snack-o-saurus/TPDA-SpaceArcade/Documentation/Pictures/nerfcomplete2.jpeg

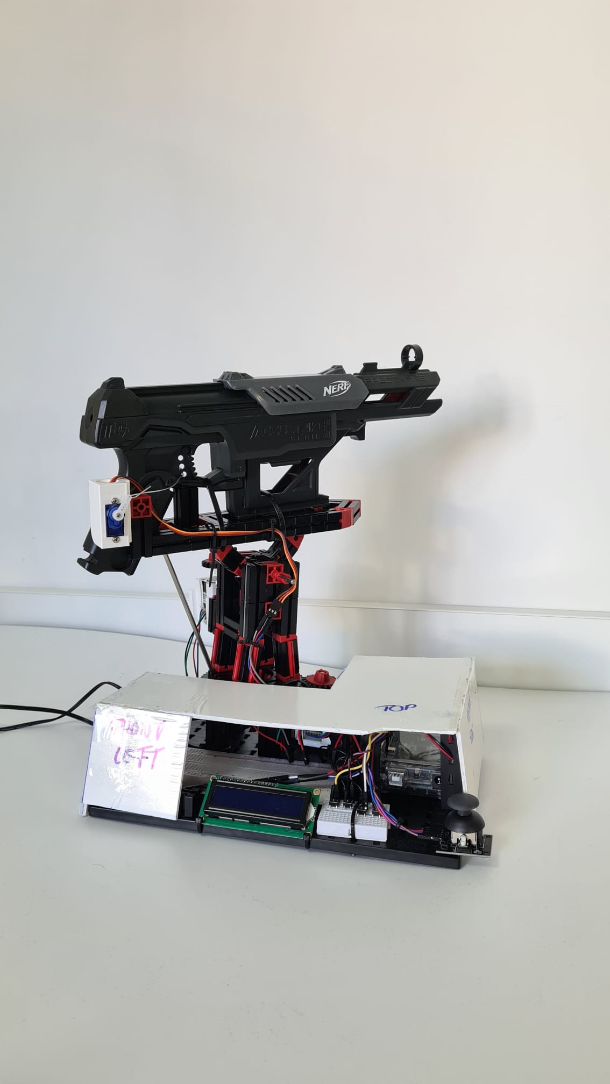
Documentation/Pictures/nerfcomplete2.jpeg
