snack-o-saurus/TPDA-SpaceArcade/Documentation/Pictures/nerfcomplete3.jpeg

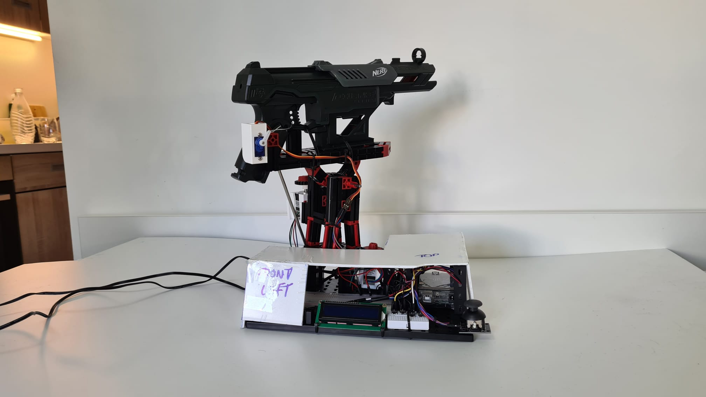
Documentation/Pictures/nerfcomplete3.jpeg
