snack-o-saurus/TPDA-SpaceArcade/Documentation/Pictures/Teiletest aus dem Druck-1/Teiltest-MEGA-1.jpeg

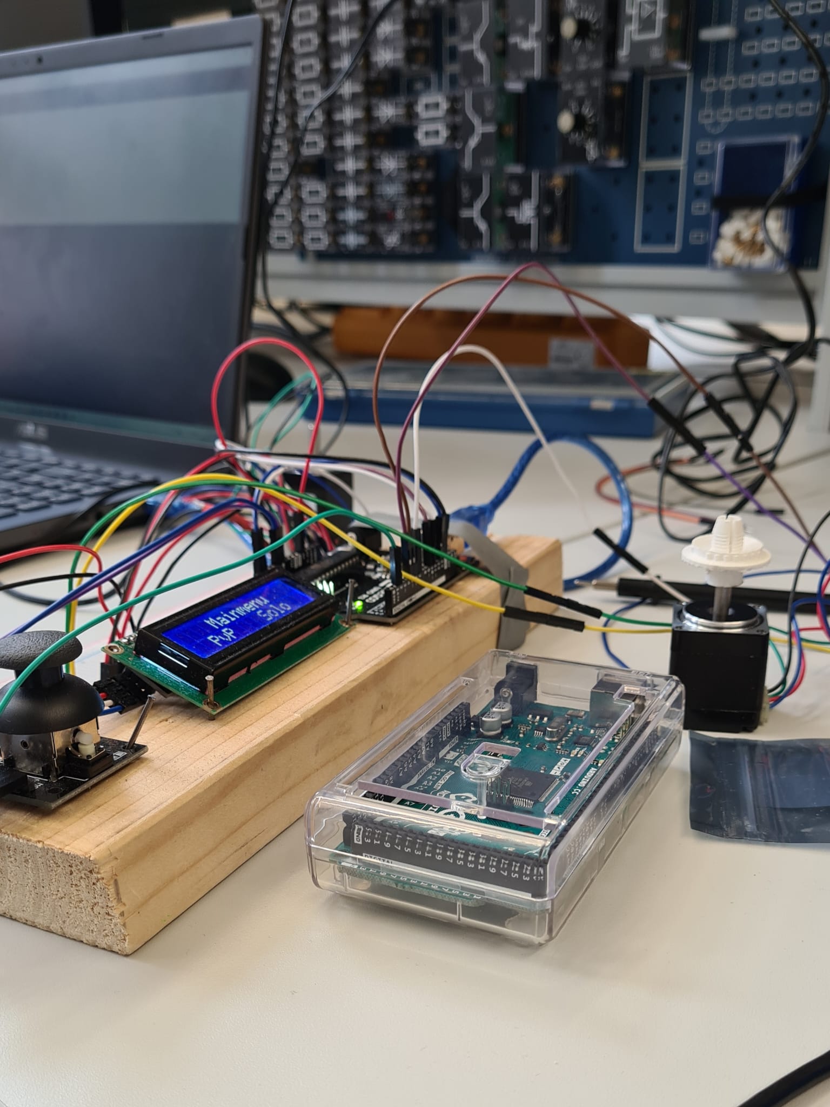
Documentation/Pictures/Teiletest aus dem Druck-1/Teiltest-MEGA-1.jpeg
