snack-o-saurus/TPDA-SpaceArcade/Documentation/Pictures/Teiletest aus dem Druck-1/Teiltest-Zahnradadapter-MEGA.jpeg

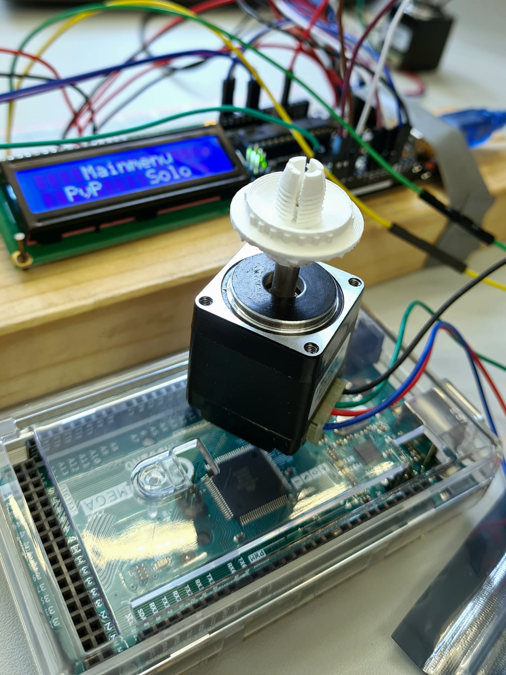
Documentation/Pictures/Teiletest aus dem Druck-1/Teiltest-Zahnradadapter-MEGA.jpeg
