snack-o-saurus/TPDA-SpaceArcade/Documentation/Pictures/Turmkonstruktion/Fischertechnik-Turret-1.jpeg

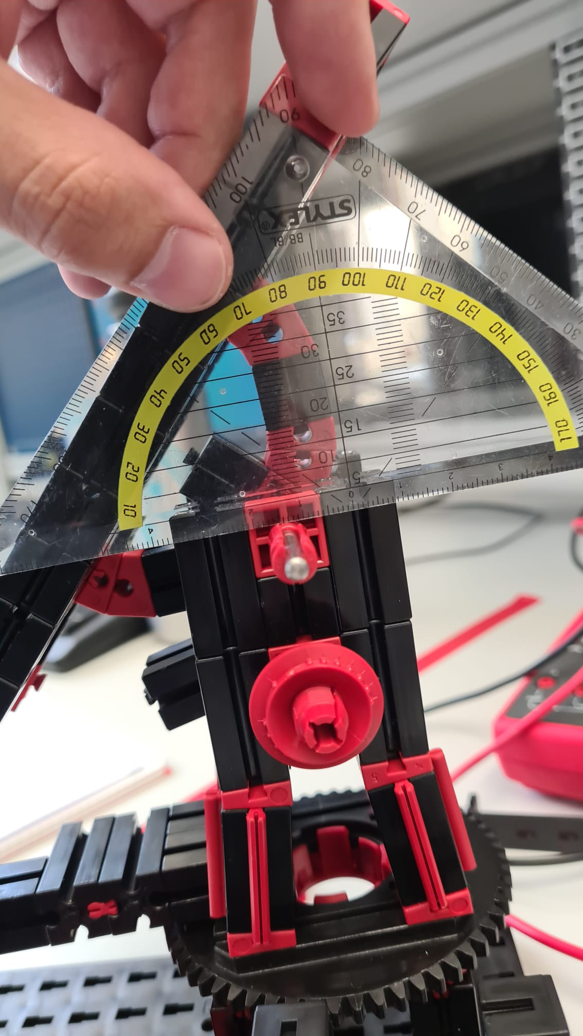
Documentation/Pictures/Turmkonstruktion/Fischertechnik-Turret-1.jpeg
