snack-o-saurus/TPDA-SpaceArcade/Documentation/Pictures/Turmkonstruktion/Fischertechnik-Turret-2.jpeg

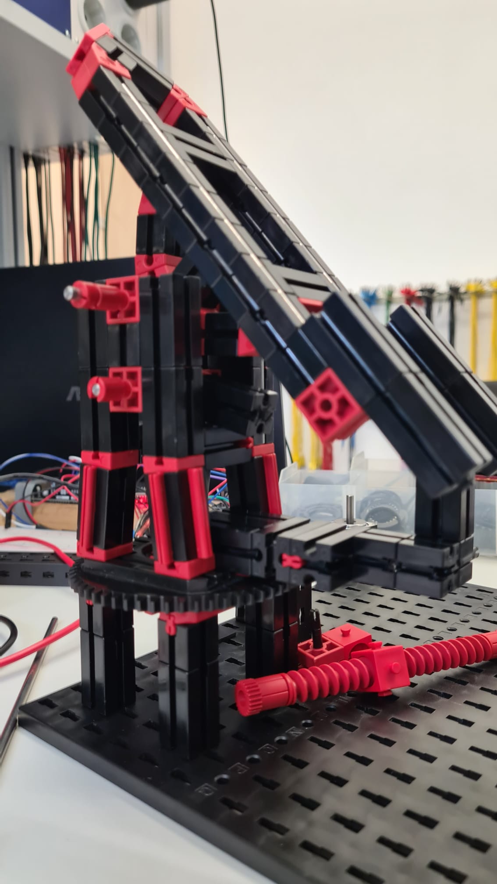
Documentation/Pictures/Turmkonstruktion/Fischertechnik-Turret-2.jpeg
