snack-o-saurus/TPDA-SpaceArcade/Documentation/Pictures/Turmkonstruktion/Fischertechnik-Turret-3.jpeg

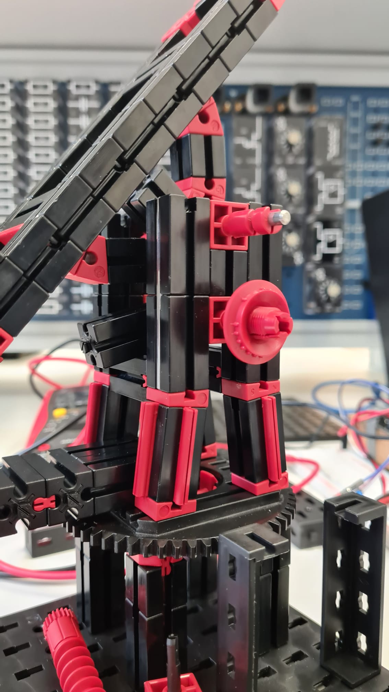
Documentation/Pictures/Turmkonstruktion/Fischertechnik-Turret-3.jpeg
