snack-o-saurus/TPDA-SpaceArcade/Documentation/Pictures/Turmkonstruktion/Fischertechnik-Turret-4.jpeg

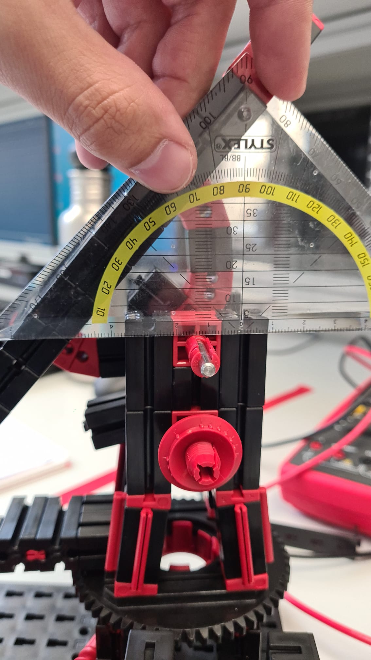
Documentation/Pictures/Turmkonstruktion/Fischertechnik-Turret-4.jpeg
