snack-o-saurus/TPDA-SpaceArcade/models/Druck01_v3/GCode-Sliceshot.png

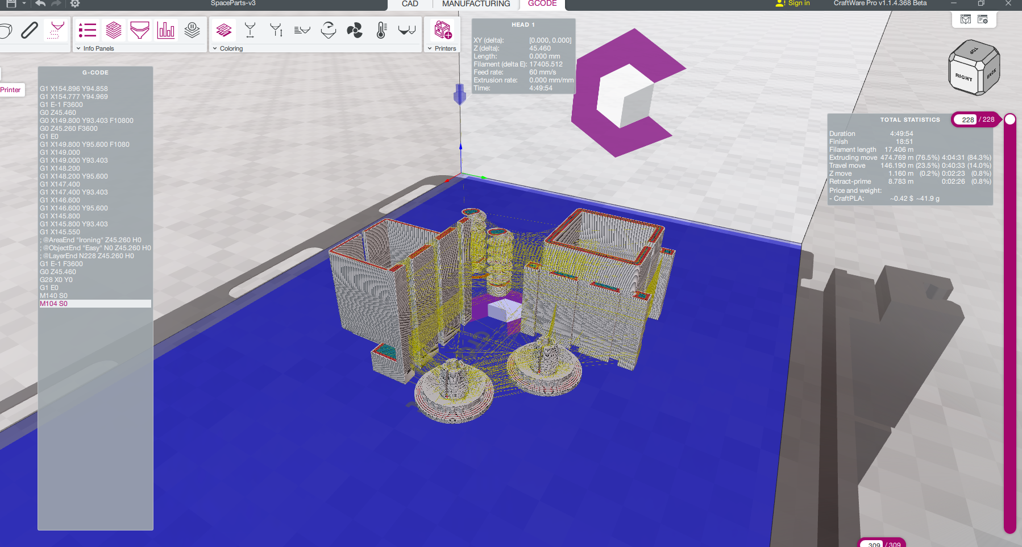
models/Druck01_v3/GCode-Sliceshot.png
