snack-o-saurus/TPDA-SpaceArcade/models/Druck01_v3/MotorPAN-case_2022-Jun-07_10-06-19AM-000_CustomizedView7136299601.png

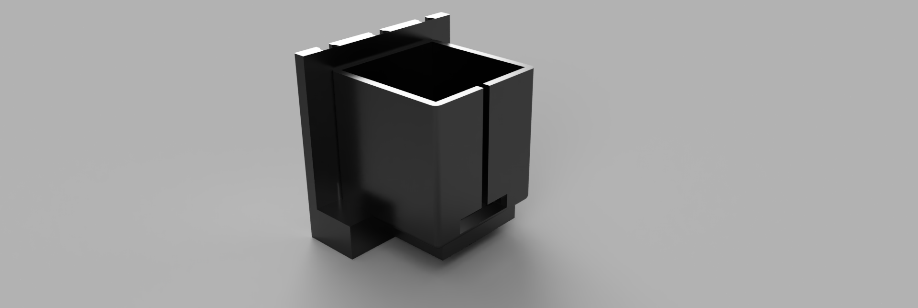
models/Druck01_v3/MotorPAN-case_2022-Jun-07_10-06-19AM-000_CustomizedView7136299601.png
