snack-o-saurus/TPDA-SpaceArcade/models/Druck01_v3/PartSummary-Render-TILT.PNG

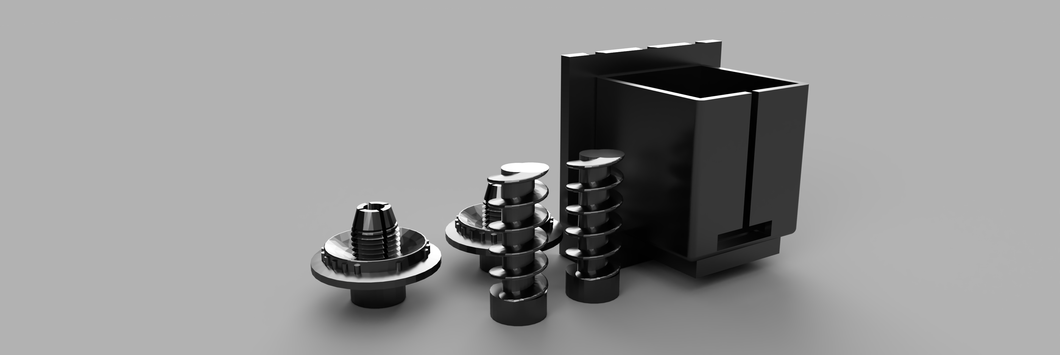
models/Druck01_v3/PartSummary-Render-TILT.PNG
