snack-o-saurus/TPDA-SpaceArcade/models/Druck02_v3/Nerfhalter-Render.PNG

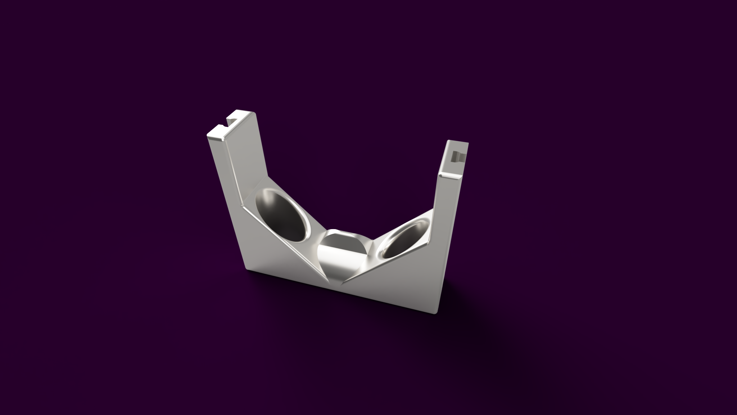
models/Druck02_v3/Nerfhalter-Render.PNG
