snack-o-saurus/TPDA-SpaceArcade/models/Druck02_v3/Servohalter-MultiRender.PNG

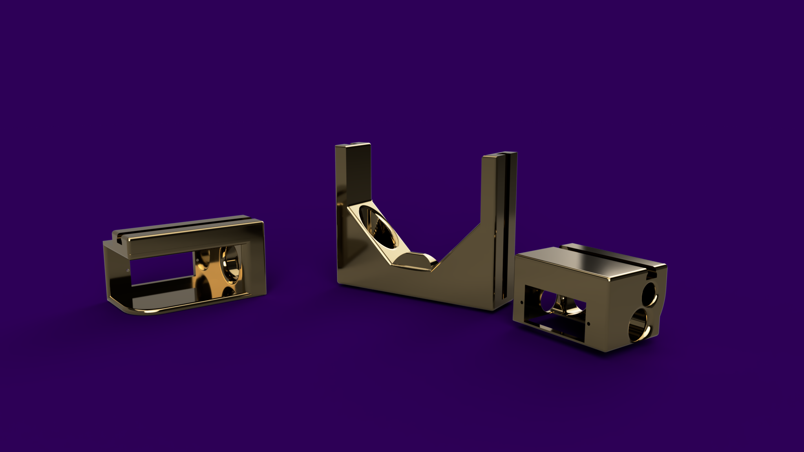
models/Druck02_v3/Servohalter-MultiRender.PNG
