snack-o-saurus/TPDA-SpaceArcade/models/Prototype #1/NerfTurret-ProTyp_v1_2022-Jun-21_01-12-33PM-000_CustomizedView25232287924.png

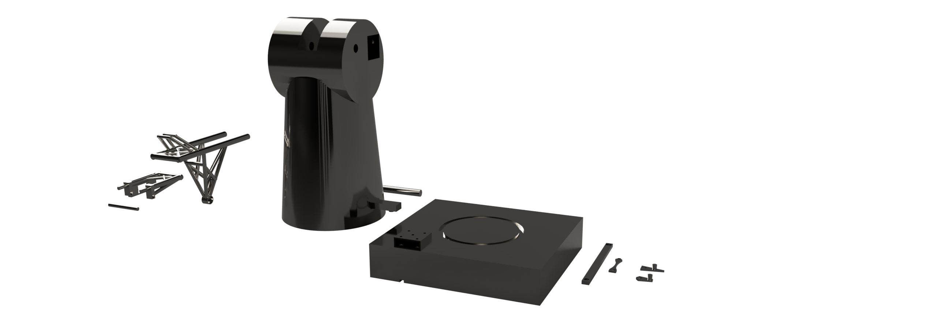
models/Prototype #1/NerfTurret-ProTyp_v1_2022-Jun-21_01-12-33PM-000_CustomizedView25232287924.png
