snack-o-saurus/TPDA-SpaceArcade/schematic/61B0OLozrOL._SL1000_.jpg

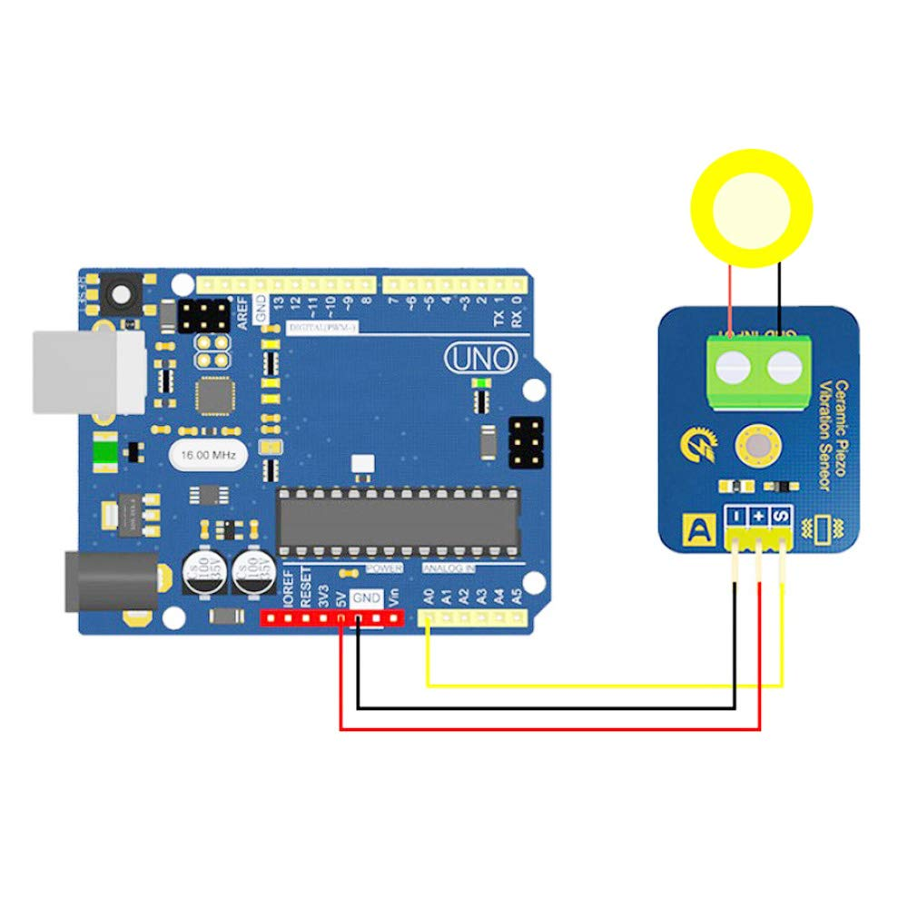
schematic/61B0OLozrOL._SL1000_.jpg
