snack-o-saurus/TPDA-SpaceArcade/schematic/SpaceInvaders-Arcade-scheme-STAGE2_Steckplatine.png

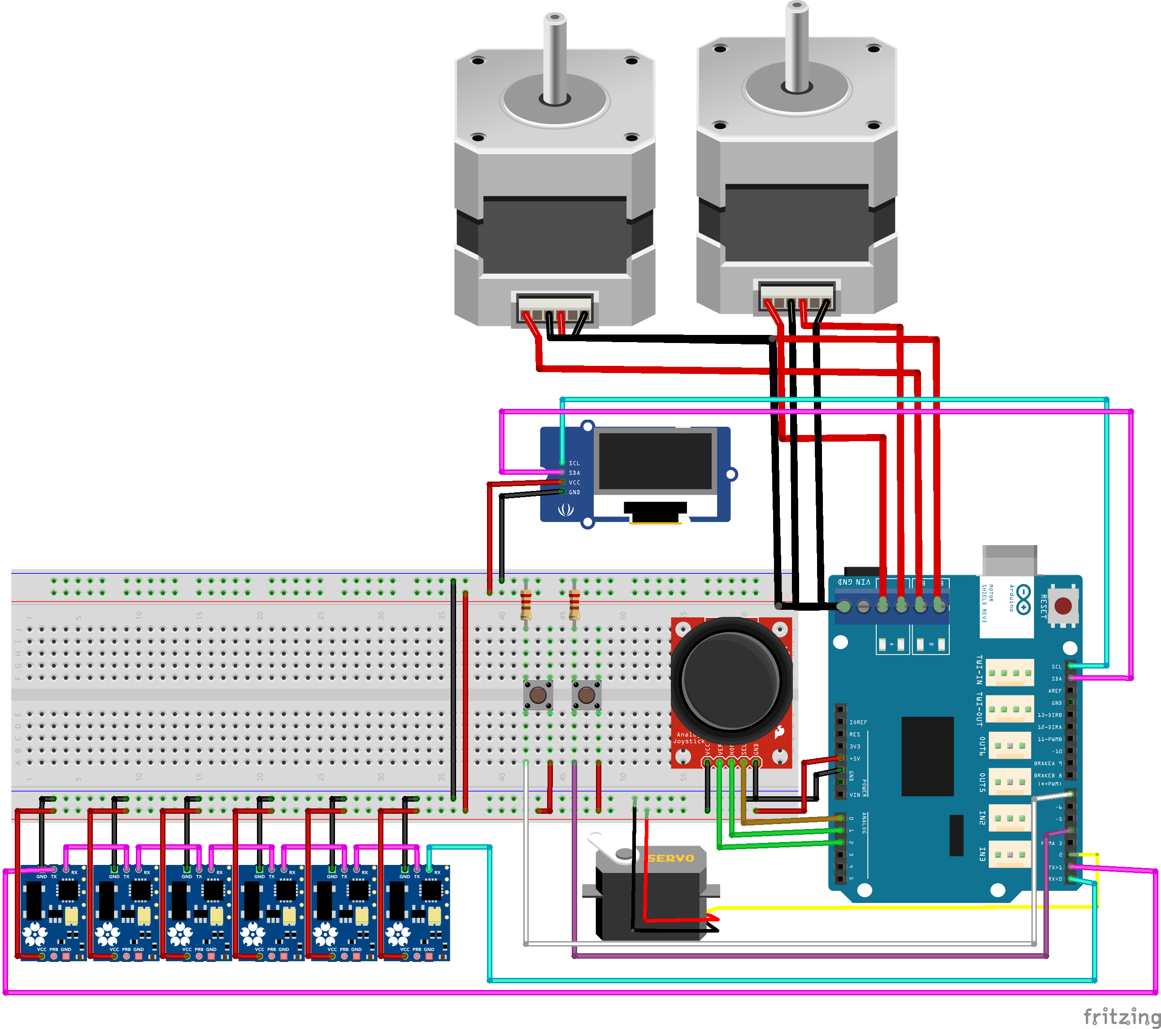
schematic/SpaceInvaders-Arcade-scheme-STAGE2_Steckplatine.png
