snack-o-saurus/TPDA-SpaceArcade/schematic/SpaceInvaders-Arcade-scheme_Kabelz.png

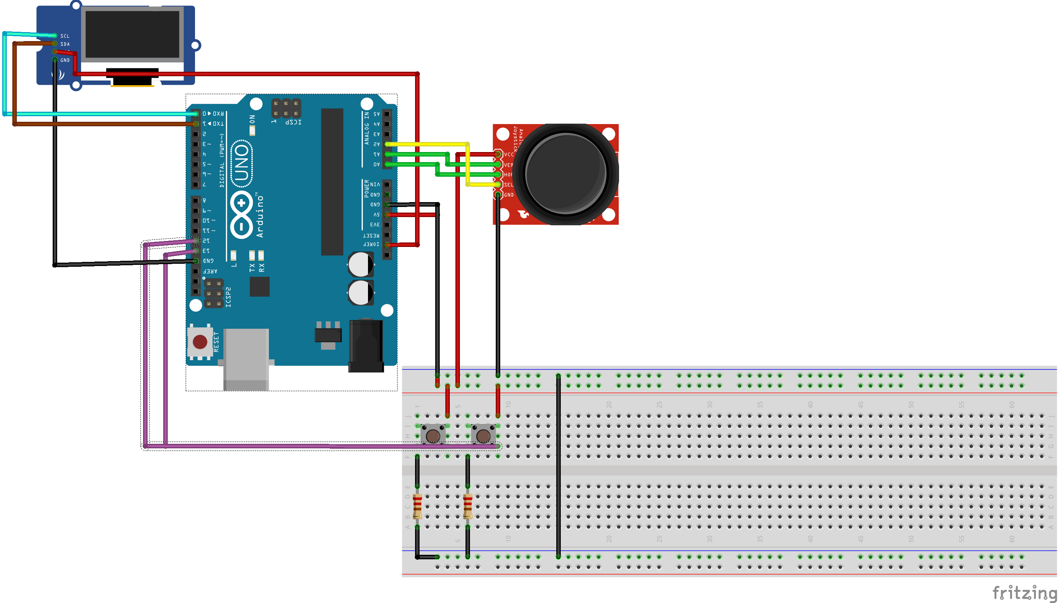
schematic/SpaceInvaders-Arcade-scheme_Kabelz.png
