snack-o-saurus/TPDA-SpaceArcade/schematic/SpaceInvaders-Arcade-scheme_PNG.png

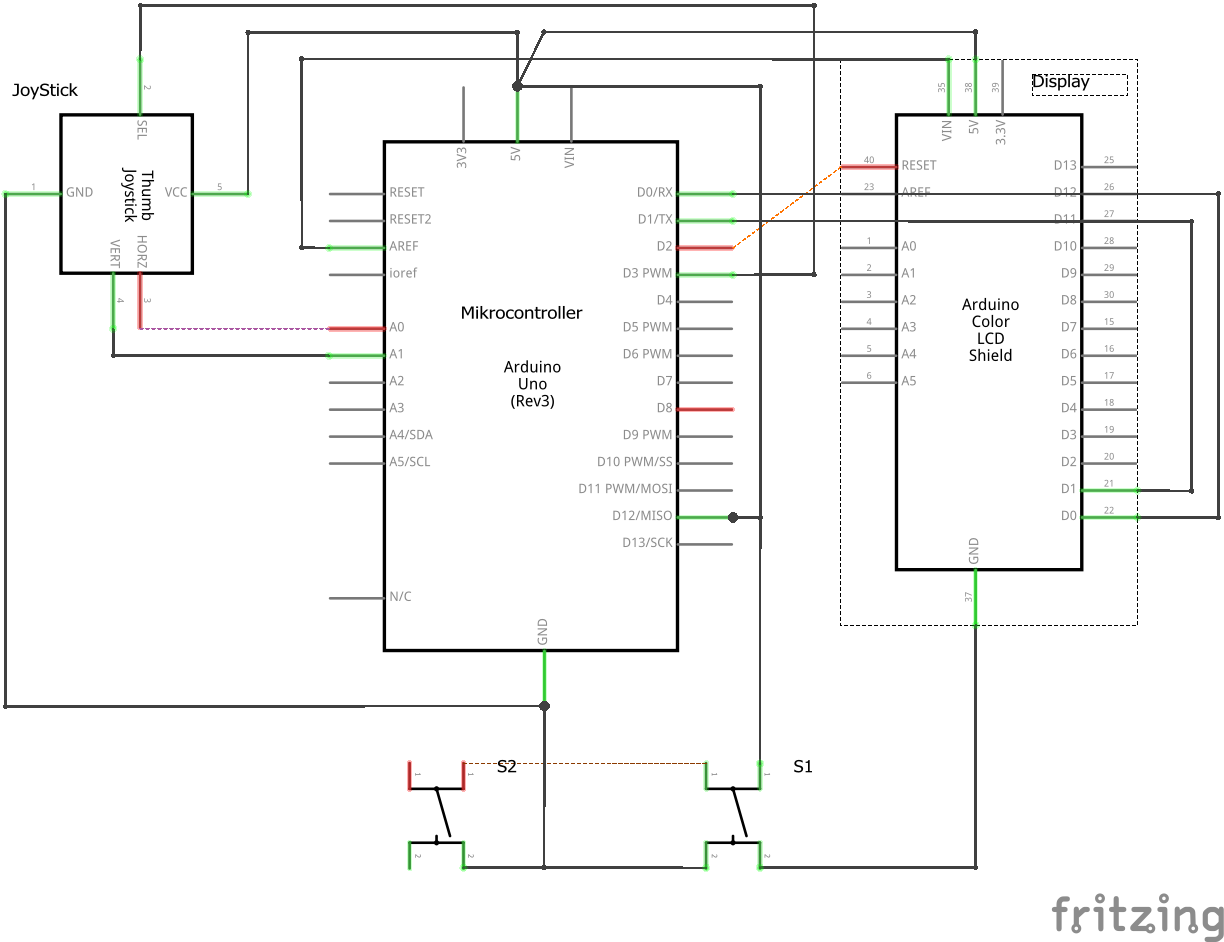
schematic/SpaceInvaders-Arcade-scheme_PNG.png
