snack-o-saurus/TPDA-SpaceArcade/TMC2208-Arduino-Driver-master/TMC2208-schematic.png

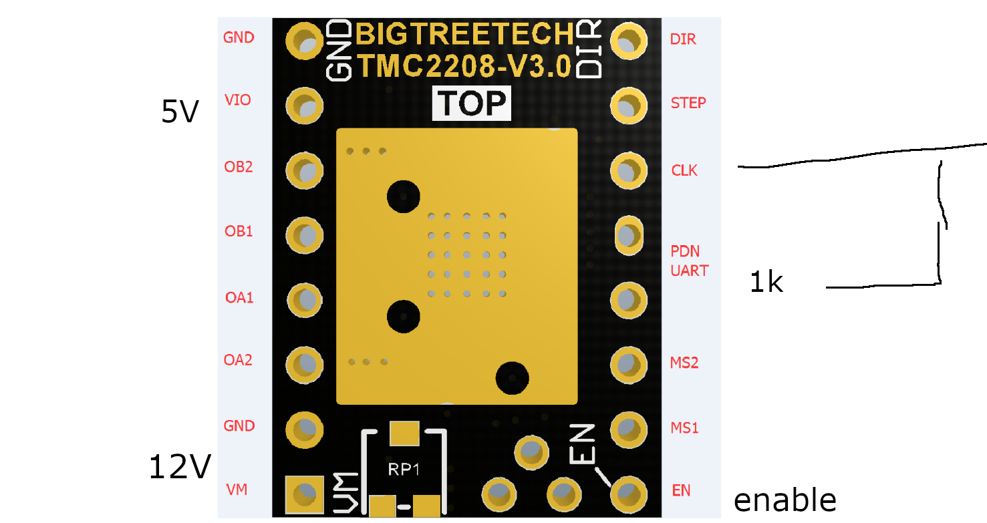
TMC2208-Arduino-Driver-master/TMC2208-schematic.png
