snack-o-saurus/TPDA-SpaceArcade/models/Druck01_v3/PrintingParts-total.png

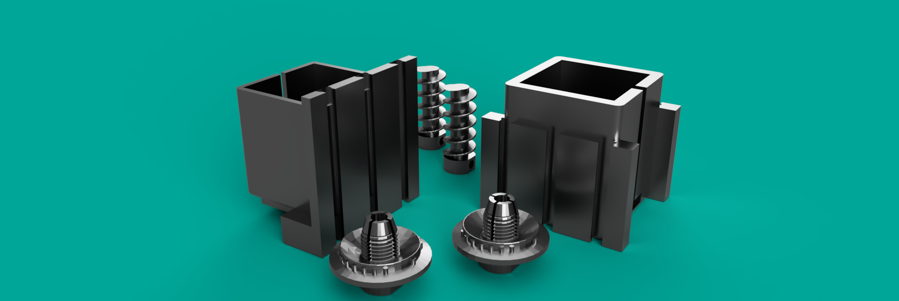
models/Druck01_v3/PrintingParts-total.png
