snack-o-saurus/TPDA-SpaceArcade/models/Prototype #1/NerfTurret-ProTyp-GP-1.stl

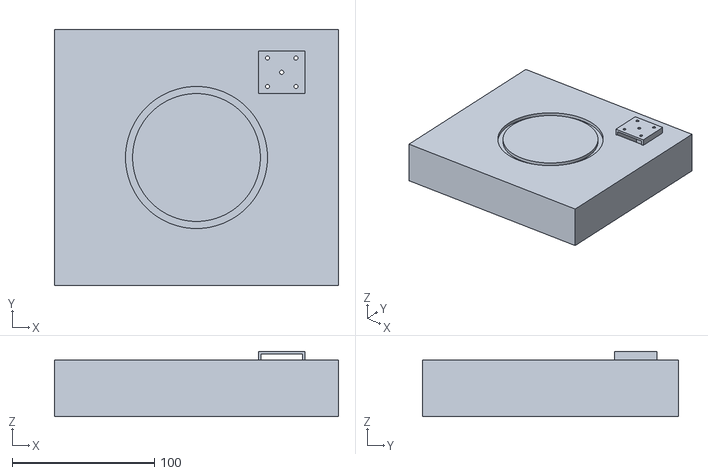
[picture p48: CAD file, 2022-05-11]
models/Prototype #1/NerfTurret-ProTyp-GP-1.stl
200.0 x 180.0 x 46.0
