snack-o-saurus/TPDA-SpaceArcade/models/Prototype #1/NerfTurret-ProTyp.stl

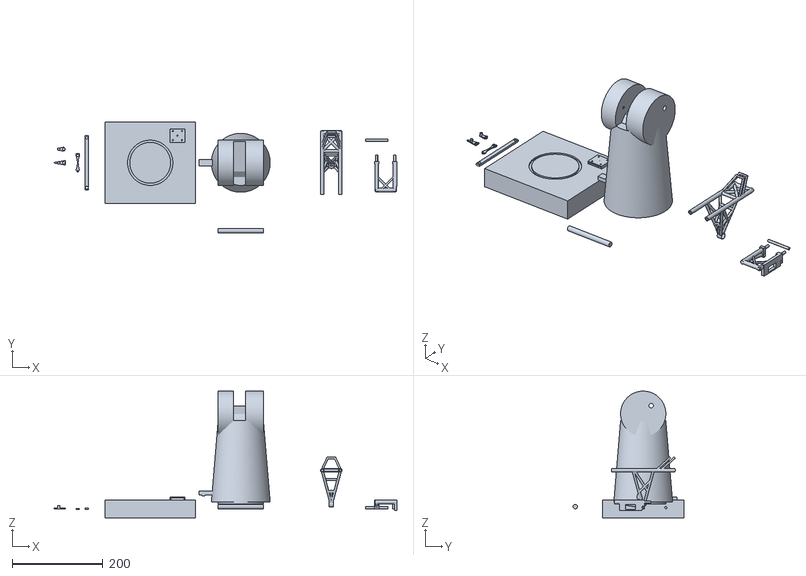
[picture p49: CAD file, 2022-04-26]
models/Prototype #1/NerfTurret-ProTyp.stl
757.5 x 245.0 x 280.0
