snack-o-saurus/TPDA-SpaceArcade/models/Prototype #1/NerfTurret-ProTyp-Turret-2.stl

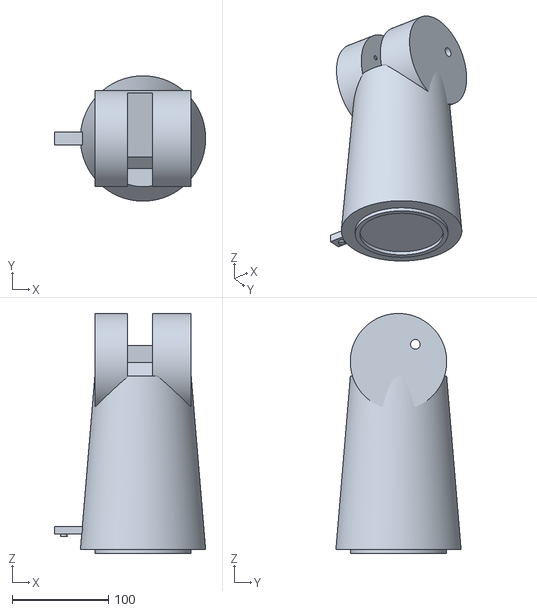
[picture p50: CAD file, 2022-05-11, an earlier design]
models/Prototype #1/NerfTurret-ProTyp-Turret-2.stl
157.0 x 130.0 x 249.0
