snack-o-saurus/TPDA-SpaceArcade/Documentation/Testen-der-Schaltung-01.jpeg

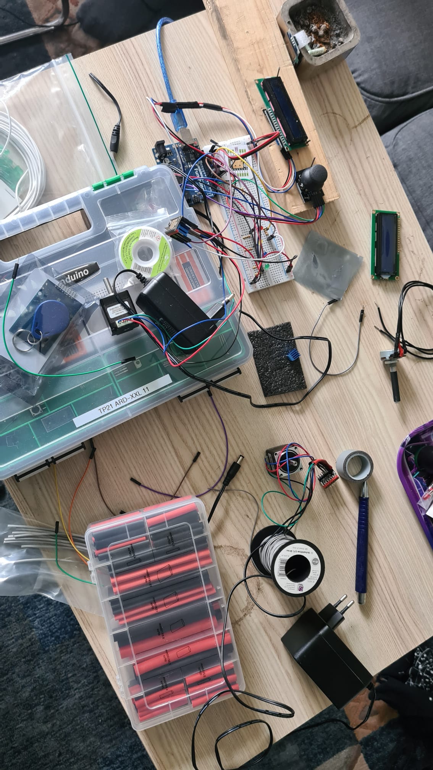
Documentation/Testen-der-Schaltung-01.jpeg
