snack-o-saurus/TPDA-SpaceArcade/Documentation/Testen-der-Schaltung-03.jpeg

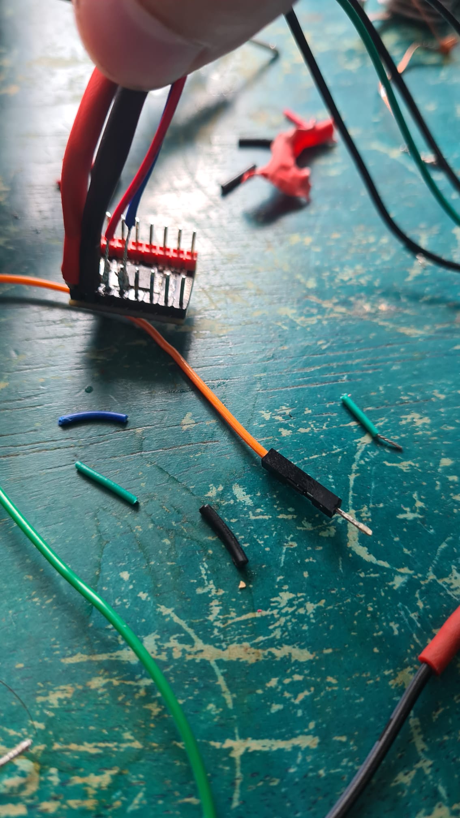
Documentation/Testen-der-Schaltung-03.jpeg
