snack-o-saurus/TPDA-SpaceArcade/Documentation/Testen-der-Schaltung-04.jpeg

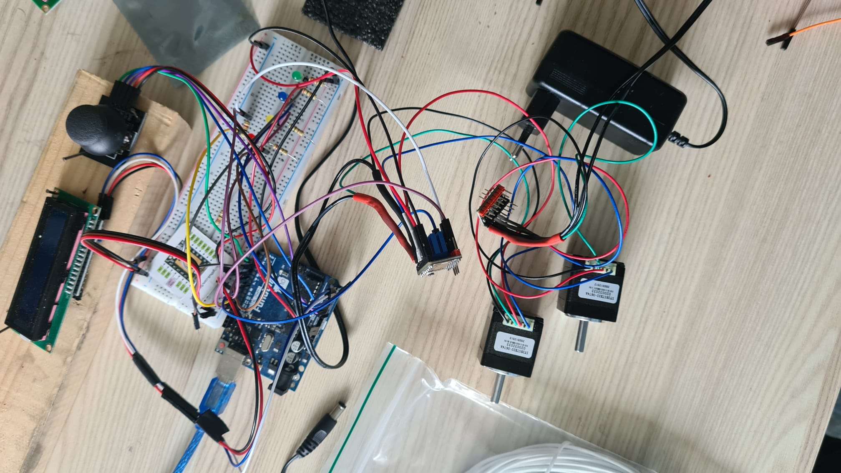
Documentation/Testen-der-Schaltung-04.jpeg
