snack-o-saurus/TPDA-SpaceArcade/Documentation/Testen-der-Schaltung-05.jpeg

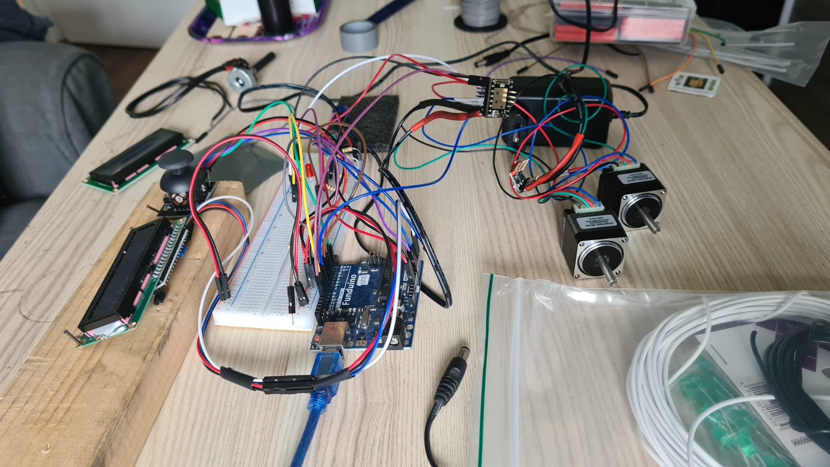
Documentation/Testen-der-Schaltung-05.jpeg
