snack-o-saurus/TPDA-SpaceArcade/schematic/SpaceArcade-schematic/SpaceArcade-schematic.kicad_sch

## KiCad design schematic/SpaceArcade-schematic/SpaceArcade-schematic.kicad_sch (2022-05-24, an earlier design)

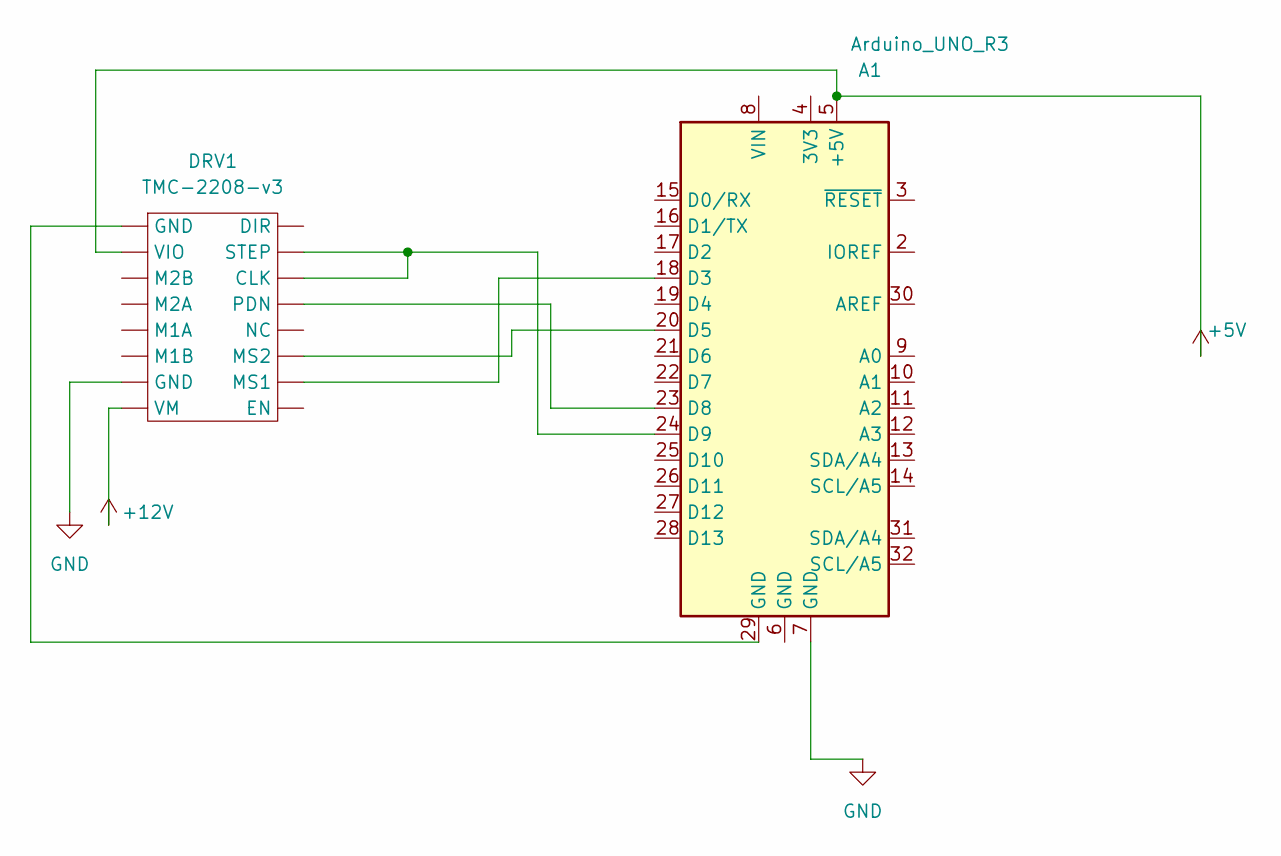
[picture p58: schematic SpaceArcade-schematic.kicad_sch]

Parts:
A1: Arduino_UNO_R3
DRV1: TMC-2208-v3

Connections:
unnamed: A1.5 (+5V), DRV1.
unnamed: A1.18 (D3), DRV1.
unnamed: A1.20 (D5), DRV1.
unnamed: A1.23 (D8), DRV1.
unnamed: A1.24 (D9), DRV1.
unnamed: A1.29 (GND), DRV1.
