snack-o-saurus/TPDA-SpaceArcade/Space-InvaderV1.1/Function.h

#include "Classes.h"
#include "Variable.h"

void mainmenu(Gameobject * object) {
  if (!start) {
    object -> getMotion();
    object -> motion();
    switch (object -> _Dir) {
      case LEFT:
        lcd.setCursor(0, 0);
        lcd.print("-Press RED Button-");
        lcd.setCursor(1, 1);
        lcd.print("[PvP]   Solo");
        if (button1.isPressed()) {             //initiate Verus-MOD
          lcd.clear();
          digitalWrite(EN_PIN_PAN, LOW);
          digitalWrite(EN_PIN_TILT, LOW);
          Serial.println("Button pressed");
          start = true;
          menutime = millis();
          return menutime;
        }
        break;
      case RIGHT:
        lcd.setCursor(0, 0);
        lcd.print("-Press RED Button-");
        lcd.setCursor(2, 1);
        lcd.print(String("PvP   [Solo]"));
        if (button1.isPressed()) {            //initiate Solo-MOD
          lcd.clear();
          Serial.println("Button pressed");
          digitalWrite(EN_PIN_PAN, LOW);
          digitalWrite(EN_PIN_TILT, LOW);
          start = true;
          solo = true;          //abfrage ob solo true ist muss noch gebaut werden
          menutime = millis();
          return menutime;
        }
        break;
      default:
        lcd.clear();
        lcd.setCursor(4, 0);
        lcd.print("Mainmenu");
        lcd.setCursor(2, 1);
        lcd.print("PvP    Solo");
        delay(50);
        break;
    }
  }
}
void runtime() {
  if (start) {
    playtime = millis();
    playtime = (playtime - menutime) / 1000;
    Serial.println("InGame-Time: ");
    Serial.println(playtime);
  }
}
void pullTrigger() {
  if (button1.isPressed() || button2.isPressed()) {
    Serial.println(button1State);
    Serial.println(button2State);
    servo.write(180);
    delay(300);
    servo.write(90);
  }
}
/*
  void singleplayer() {
  // all functions explicitly for singleplayer belong here
  }
  void multiplayer() {
  // all functions explicitly for multiplayer belong here
  }
*/



void enterName(Gameobject * object) {
    lcd.setCursor(0, 0);
    lcd.print("Enter your Name");
    if(object -> getDir() == DOWN ){
      i++;
      delay(1000);
    }
    if(object -> getDir() == UP){
      i--;
      delay(1000);
    }
      lcd.setCursor(1, 3 + j);                            // Eingabeart ist noch nicht klar!!(vielleicht Buchstaben A-Z pro Zeichen durchlaufen und mit Button bestätigen und zur nächsten Stelle springen
      lcd.print(arrayLetters[i]);
      delay(1000);
      if (button1.isPressed()) {
        tempName[j] = arrayLetters[i];                    // Einzelne Buchstaben des Arrays in id übertragen in einen String speichern
        // lcd.print(arrayLetters[i]);
        j++;
        return j;
      }
      if (j == 8) {
        lcd.setCursor(2, 1);
        lcd.print("Saving ID...");
        for (z = 0; z <= 8; z++) {
          object -> setId( object-> getId() + tempName[z]);
        }
      }
      if (i == 25) {
        i = 0;
      }
    }


void rulerSOLO() {
  switch (difficulty) {
    case SLOW:
      lcd.setCursor(1, 5);
      lcd.print("-[SLOW]-");
      if (playtime >= 300) {
        lcd.clear();
        lcd.setCursor(0, 3);
        lcd.print("-Game Over-");
        gameover = true;
      }
      break;
    case REGULAR:
      lcd.setCursor(1, 5);
      lcd.print("-[SLOW]-");
      if (playtime >= 180) {
        lcd.clear();
        lcd.setCursor(0, 3);
        lcd.print("-Game Over-");
        gameover = true;
      }
      break;
    case FAST:
      lcd.setCursor(1, 5);
      lcd.print("-[SLOW]-");
      if (playtime >= 90) {
        lcd.clear();
        lcd.setCursor(0, 3);
        lcd.print("-Game Over-");
        gameover = true;
      }
      break;
  }
}


void selectMod(Gameobject * object) {
  lcd.setCursor(0, 0);
  lcd.print("Select Mod");
  if (object -> getDir() == UP) {
    lcd.clear();
    difficulty++;
    if (difficulty <= 0) {
      difficulty = 3;
    }
    
  }
  else if (object -> getDir() == DOWN) {
    lcd.clear();
    difficulty--;
    if (difficulty >= 4) {
      difficulty = 1;
    }
  if(button1.isPressed()){
    
  }
  }



}
